planmarks/Spunkleboard/Firmwares/Splunkagotchi/sprites.h

// =============================================================================
//  sprites.h  -  Creature + HUD bitmaps (Lopaka-exported, ported to Adafruit).
//  All bitmaps are 1bpp, MSB-first, byte-aligned rows -> Adafruit_GFX
//  drawBitmap(x, y, bits, w, h, color) format.
//  Renamed per-stage so symbols don't collide.
// =============================================================================
#pragma once
#include <Arduino.h>

// ---- HUD icons --------------------------------------------------------------
// Small device/BLE glyph (5x8) and Wi-Fi glyph (9x7).
static const unsigned char PROGMEM ic_dev_bits[]  = {
  0x20,0x30,0xa8,0x70,0x70,0xa8,0x30,0x20
};
static const unsigned char PROGMEM ic_wifi_bits[] = {
  0x3e,0x00,0x41,0x00,0x80,0x80,0x1c,0x00,0x22,0x00,0x00,0x00,0x08,0x00
};

// ---- Baby (three parts) -----------------------------------------------------
static const unsigned char PROGMEM baby_body_bits[] = {  // 26 x 27
  0x03,0xff,0xe0,0x00,0x0e,0x00,0x30,0x00,0x18,0x00,0x1c,0x00,0x30,0x00,0x06,0x00,
  0x20,0x00,0x03,0x00,0x20,0x00,0x01,0x00,0x20,0x00,0x01,0x80,0x20,0x00,0x00,0x80,
  0x20,0x00,0x00,0x80,0x20,0x00,0x00,0x80,0x20,0x00,0x00,0x80,0x20,0x00,0x00,0x80,
  0x60,0x00,0x00,0x80,0x40,0x00,0x00,0x80,0x40,0x00,0x01,0x80,0x40,0x00,0x01,0x00,
  0x40,0x00,0x01,0x00,0x40,0x00,0x01,0x00,0x40,0x00,0x01,0x00,0x40,0x00,0x01,0x00,
  0x60,0x00,0x00,0x40,0x50,0x40,0x44,0x40,0xc0,0x80,0x4a,0x00,0x81,0x80,0x30,0x00,
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
  0x80,0x00,0x00,0x10,0x00,0x1c,0x00,0x80,0x00,0x00,0x00,0x00,0x02,0x00,0x80,0x00,
  0x00,0x00,0x00,0x01,0x00,0xc0,0x00,0x00,0x00,0x00,0x01,0x00,0x40,0x00,0x00,0x00,
  0x00,0x00,0x80,0x60,0x00,0x00,0x00,0x00,0x00,0x80,0x30,0x00,0x00,0x00,0x00,0x00,
  0x80,0x1c,0x00,0x00,0x00,0x00,0x01,0x00,0x07,0xff,0xff,0xff,0xff,0xff,0x00
};
